igrow-systems/igrow-hardware/igrow-101/Draft1.asc

D1: LED
Q1: npn
R1: res; 10
R2: res; 100k
V1: voltage; 3; Rser=20
V2: voltage; 3; Rser=1
Named nets: 0
