igrow-systems/igrow-hardware/sim/leds/led_outputs_green_single_bjt.asc

D1: LED; NSCW100
Q1: npn; BC847C
R1: res; 0
R2: res; 100k
V1: voltage; 3; Rser=20
V2: voltage; 2.7; Rser=10
Named nets: 0
.inc LNJ953W8CRA.lib
.dc V1 3.1 2.7
